M-Mrk/Attention-Seeker/case/bottom-case.png

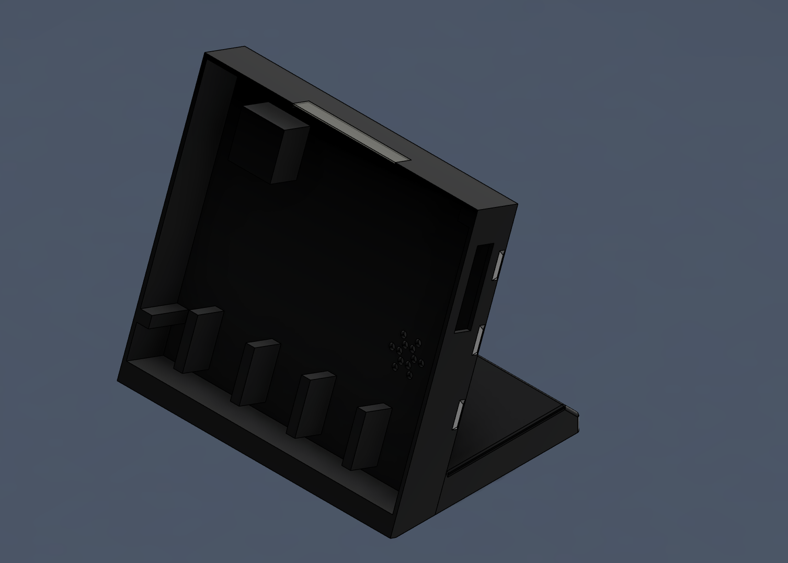
case/bottom-case.png
