M-Mrk/Attention-Seeker/case/pcb-in-case.png

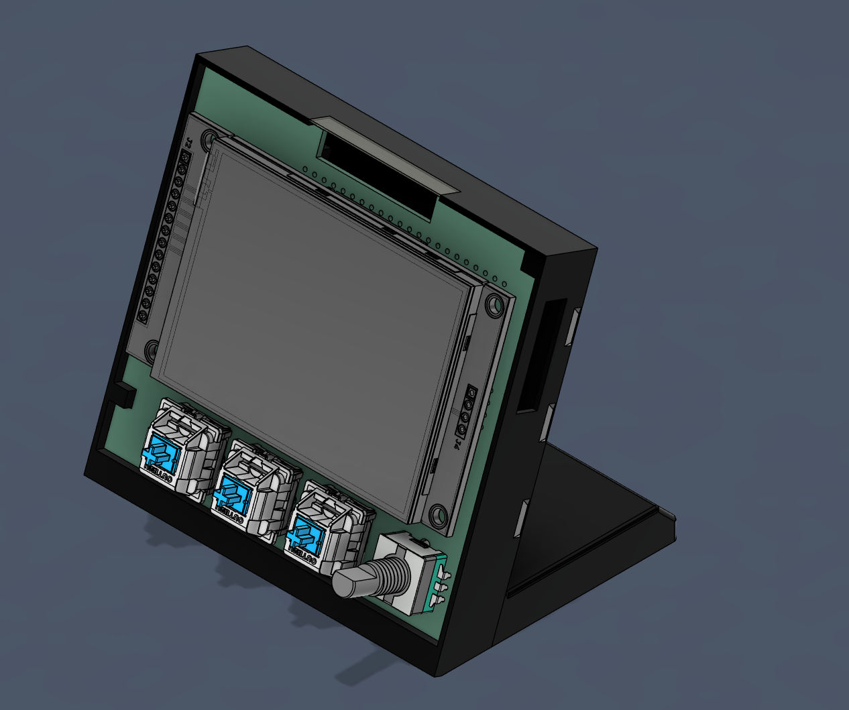
case/pcb-in-case.png
